datdo-is-coding/Home-Assistant-IoT-/Hardware/PCB/IoT_Board/erc_report.txt

ERC report (2026-08-20T07:09:29, Encoding UTF8)
Report includes: Errors, Warnings, Exclusions

***** Sheet /
[power_pin_not_driven]: Input Power pin not driven by any Output Power pins
    ; error
    @(25.40 mm, 194.31 mm): Symbol #PWR084 Pin 1 [Power input, Line]
[power_pin_not_driven]: Input Power pin not driven by any Output Power pins
    ; error
    @(80.01 mm, 100.33 mm): Symbol #PWR02 Pin 1 [Power input, Line]
[power_pin_not_driven]: Input Power pin not driven by any Output Power pins
    ; error
    @(309.88 mm, 248.92 mm): Symbol #PWR050 Pin 1 [Power input, Line]
[power_pin_not_driven]: Input Power pin not driven by any Output Power pins
    ; error
    @(377.19 mm, 243.84 mm): Symbol U4 Pin 1 [AC/L, Power input, Line]
[power_pin_not_driven]: Input Power pin not driven by any Output Power pins
    ; error
    @(377.19 mm, 248.92 mm): Symbol U4 Pin 2 [AC/N, Power input, Line]
[power_pin_not_driven]: Input Power pin not driven by any Output Power pins
    ; error
    @(401.32 mm, 191.77 mm): Symbol #PWR020 Pin 1 [Power input, Line]
[same_local_global_label]: Local and global labels have same name
    ; warning
    @(38.10 mm, 171.45 mm): Global Label 'RS'
    @(55.88 mm, 77.47 mm): Label 'RS'
[same_local_global_label]: Local and global labels have same name
    ; warning
    @(40.64 mm, 166.37 mm): Global Label 'CS'
    @(55.88 mm, 80.01 mm): Label 'CS'
[same_local_global_label]: Local and global labels have same name
    ; warning
    @(40.64 mm, 196.85 mm): Global Label 'DIN'
    @(55.88 mm, 82.55 mm): Label 'DIN'
[same_local_global_label]: Local and global labels have same name
    ; warning
    @(40.64 mm, 199.39 mm): Global Label 'SCLK'
    @(55.88 mm, 85.09 mm): Label 'SCLK'
[footprint_link_issues]: The current configuration does not include the footprint library 'ADS'
    ; warning
    @(69.85 mm, 194.31 mm): Symbol U14 [ADS1256IDBR]
[same_local_global_label]: Local and global labels have same name
    ; warning
    @(96.52 mm, 166.37 mm): Global Label 'DRDY'
    @(55.88 mm, 90.17 mm): Label 'DRDY'
[same_local_global_label]: Local and global labels have same name
    ; warning
    @(96.52 mm, 168.91 mm): Global Label 'DO'
    @(55.88 mm, 87.63 mm): Label 'DO'
[multiple_net_names]: Both VREFP and V_Bias are attached to the same items; VREFP will be used in the netlist
    ; warning
    @(36.83 mm, 204.47 mm): Label 'VREFP'
    @(127.00 mm, 148.59 mm): Label 'V_Bias'
[lib_symbol_mismatch]: Symbol 'Conn_01x07_Pin' doesn't match copy in library 'Connector'
    ; warning
    @(182.88 mm, 67.31 mm): Symbol J14 [Conn_01x07_Pin]
[lib_symbol_mismatch]: Symbol 'Conn_02x03_Counter_Clockwise' doesn't match copy in library 'Connector_Generic'
    ; warning
    @(191.77 mm, 91.44 mm): Symbol J15 [Conn_02x03_Counter_Clockwise]
[footprint_link_issues]: The current configuration does not include the footprint library ''
    ; warning
    @(232.41 mm, 29.21 mm): Symbol IC1 [VS1838B]
[footprint_link_issues]: The current configuration does not include the footprint library 'B050S'
    ; warning
    @(309.88 mm, 241.30 mm): Symbol PS1 [B0505S-2W]
[footprint_link_issues]: The current configuration does not include the footprint library 'PC817_SMD'
    ; warning
    @(316.23 mm, 38.10 mm): Symbol U7 [PC817]
[footprint_link_issues]: The current configuration does not include the footprint library 'PC817_SMD'
    ; warning
    @(317.50 mm, 74.93 mm): Symbol U6 [PC817]
[footprint_link_issues]: The current configuration does not include the footprint library 'PC817_SMD'
    ; warning
    @(317.50 mm, 114.30 mm): Symbol U5 [PC817]
[footprint_link_issues]: The current configuration does not include the footprint library 'RL10SRD'
    ; warning
    @(369.57 mm, 29.21 mm): Symbol K3 [SRD-12VDC-SL-C]
[lib_symbol_issues]: The current configuration does not include the symbol library 'RL10ASRD'
    ; warning
    @(369.57 mm, 29.21 mm): Symbol K3 [SRD-12VDC-SL-C]
[footprint_link_issues]: The current configuration does not include the footprint library 'RL10SRD'
    ; warning
    @(370.84 mm, 66.04 mm): Symbol K2 [SRD-12VDC-SL-C]
[lib_symbol_issues]: The current configuration does not include the symbol library 'RL10ASRD'
    ; warning
    @(370.84 mm, 66.04 mm): Symbol K2 [SRD-12VDC-SL-C]
[footprint_link_issues]: The current configuration does not include the footprint library 'RL10SRD'
    ; warning
    @(370.84 mm, 105.41 mm): Symbol K1 [SRD-12VDC-SL-C]
[lib_symbol_issues]: The current configuration does not include the symbol library 'RL10ASRD'
    ; warning
    @(370.84 mm, 105.41 mm): Symbol K1 [SRD-12VDC-SL-C]
[multiple_net_names]: Both +5VD and USB_V are attached to the same items; +5VD will be used in the netlist
    ; warning
    @(248.92 mm, 57.15 mm): Symbol #PWR0116 Pin 1 [Power input, Line]
    @(375.92 mm, 167.64 mm): Label 'USB_V'
[footprint_link_issues]: The current configuration does not include the footprint library 'KH-TYPE-C-16P'
    ; warning
    @(383.54 mm, 191.77 mm): Symbol J3 [KH-TYPE-C-16P]
[lib_symbol_issues]: The current configuration does not include the symbol library 'KH-TYPE-C-16P'
    ; warning
    @(383.54 mm, 191.77 mm): Symbol J3 [KH-TYPE-C-16P]

 ** ERC messages: 30  Errors 6  Warnings 24

 ** Ignored checks:
    - Global label only appears once in the schematic
    - Four connection points are joined together
    - SPICE model issue
    - Assigned footprint doesn't match footprint filters
