datdo-is-coding/Home-Assistant-IoT-/App/dtv_energy_flutter/test/goldens/home.png

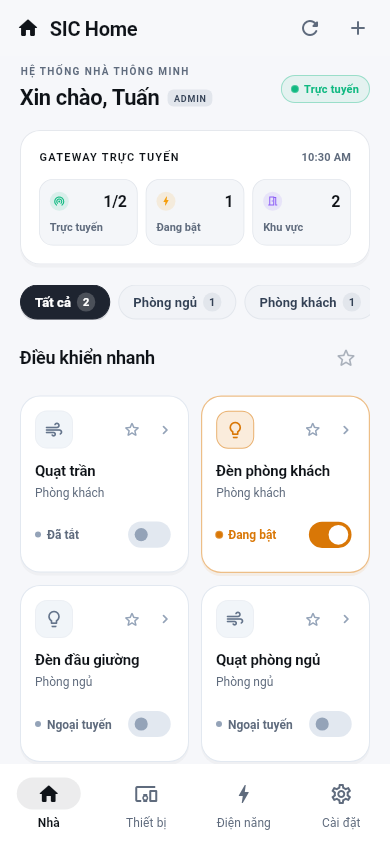
App/dtv_energy_flutter/test/goldens/home.png
