datdo-is-coding/Home-Assistant-IoT-/App/dtv_energy_flutter/test/goldens/settings.png

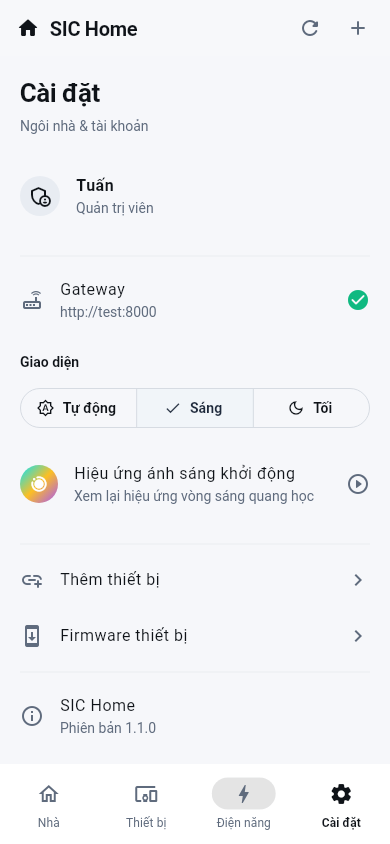
App/dtv_energy_flutter/test/goldens/settings.png
