datdo-is-coding/Home-Assistant-IoT-/Gateway/gateway/intent_engine.py

"""
Intent Engine v3 — Hệ thống phân tích ý định khẩu lệnh tiếng Việt (Production-Ready for Raspberry Pi 4)
===================================================================================================

Triết lý kiến trúc chuẩn:
    ASR ≠ Intent ≠ Device ≠ Node ≠ Execution ≠ Response

Pipeline:
    ASR text
       ↓
    ASR Normalizer (âm vị, độ tin cậy, không phá vỡ ngữ cảnh)
       ↓
    Negation Detector (chặn câu phủ định, không biến thành turn_on)
       ↓
    Fast Path / Rule Engine (phân cấp HIGH / MEDIUM / AMBIGUOUS)
       ↓ (nếu HIGH ≥ 0.95 → bypass LLM)
    Context Resolver (Multi-turn Context với TTL, kế thừa an toàn)
       ↓ (nếu cần LLM / phức tạp)
    LLM NLU Engine (Gemini Flash Cloud / Local Qwen 2.5 với prompt siêu gọn & GBNF)
       ↓
    Intent Normalization
       ↓
    Strict Validator (đối chiếu Registry: Exact → Alias → Unique Fuzzy → Reject)
       ↓
    IntentResult (Dữ liệu cấu trúc + tương thích ngược dictionary)

Nguyên tắc bất biến:
- Intent Engine KHÔNG điều khiển GPIO, KHÔNG quyết định node_id/channel
- Intent Engine KHÔNG hallucinate thiết bị/phòng ngoài Registry
- Intent Engine KHÔNG tự nhận định command thành công trước khi Verifier/MQTT trả kết quả
- Response hoàn tất ("Dạ em đã bật...") chỉ do Verifier/Response Generator sinh sau khi ESP32 thực thi
"""

import json
import logging
import re
import time
from dataclasses import dataclass, field
from typing import Optional, Dict, Any, List, Tuple

try:
    import httpx
except ImportError:
    httpx = None

import config
from display_names import get_room_name, get_device_name, clean_voice_text

logger = logging.getLogger("intent")


# ── BẢNG TỪ ĐIỂN VÀ ALIASES CHUẨN HOÁ ────────────────────────────────────────

def slug(s: Optional[str]) -> str:
    """Chuyển đổi chuỗi tiếng Việt có dấu thành slug không dấu dạng snake_case."""
    if s is None:
        return ""
    s = str(s).lower().strip()
    tbl = str.maketrans(
        "áàảãạăắằẳẵặâấầẩẫậéèẻẽẹêếềểễệíìỉĩịóòỏõọôốồổỗộơớờởỡợúùủũụưứừửữựýỳỷỹỵđ",
        "aaaaaaaaaaaaaaaaaeeeeeeeeeeeiiiiiooooooooooooooooouuuuuuuuuuuyyyyyd"
    )
    s = s.translate(tbl)
    s = re.sub(r"[^a-z0-9]+", "_", s).strip("_")
    return s


# Danh mục thiết bị chuẩn (Canonical Device Mapping)
DEVICE_ALIASES: Dict[str, List[str]] = {
    "light": [
        "đèn", "bóng đèn", "đèn điện", "ánh sáng", "light", "den", "bong_den",
        "đèn trần", "den_tran", "đèn chùm", "đèn tuýp", "đèn led", "đèn bàn", "đèn học"
    ],
    "den_ngu": [
        "đèn ngủ", "den_ngu", "đèn đầu giường", "den ngu"
    ],
    "fan": [
        "quạt", "quạt điện", "quạt máy", "quat", "fan",
        "quạt trần", "quạt cây", "quạt đứng", "quạt bàn", "quạt treo", "quạt thông gió"
    ],
    "air_conditioner": [
        "điều hòa", "máy lạnh", "máy điều hòa", "dieu_hoa", "may_lanh", "ac",
        "air conditioner", "air_conditioner", "máy lạng", "máy lặng"
    ],
    "pump": [
        "máy bơm", "bơm", "máy tưới", "tưới cây", "tưới", "pump", "may_bom"
    ],
    "curtain": [
        "rèm", "rèm cửa", "màn", "màn cửa", "curtain", "rem"
    ],
    "tivi": [
        "tivi", "ti vi", "tv", "television"
    ],
    "binh_nong_lanh": [
        "bình nóng lạnh", "bình nước nóng", "nước nóng", "binh_nong_lanh"
    ],
    "may_hut_mui": [
        "hút mùi", "máy hút mùi", "may_hut_mui", "quạt hút mùi"
    ],
    "socket": [
        "ổ cắm", "o_cam", "ổ điện", "phích cắm", "socket", "ổ", "o cam", "o dien",
        "ổ cắm điện", "phích cắm điện"
    ],
    "ch1": [
        "relay 1", "relay một", "công tắc 1", "công tắc một", "kênh 1", "kênh một", "nút 1"
    ],
    "ch2": [
        "relay 2", "relay hai", "công tắc 2", "công tắc hai", "kênh 2", "kênh hai", "nút 2"
    ],
    "all": [
        "tất cả", "toàn bộ", "hết", "toàn bộ thiết bị", "tất cả thiết bị"
    ]
}

# Danh mục phòng chuẩn (Canonical Room Mapping)
ROOM_ALIASES: Dict[str, List[str]] = {
    "phong_ngu": [
        "phòng ngủ", "phong ngu", "ngủ", "bedroom", "p_ngu"
    ],
    "phong_ngu_master": [
        "phòng ngủ master", "phòng master", "ngủ master", "master bedroom"
    ],
    "phong_ngu_con": [
        "phòng ngủ con", "ngủ con", "phòng con"
    ],
    "phong_khach": [
        "phòng khách", "phong khach", "khách", "living room", "livingroom", "p_khach"
    ],
    "phong_bep": [
        "phòng bếp", "phong bep", "bếp", "nhà bếp", "kitchen", "p_bep"
    ],
    "phong_tam": [
        "nhà vệ sinh", "vệ sinh", "toilet", "wc", "phòng tắm", "bathroom", "tắm", "phong_ve_sinh"
    ],
    "ban_cong": [
        "ban công", "balcony"
    ],
    "san_thuong": [
        "sân thượng", "rooftop"
    ],
    "san_vuon": [
        "sân vườn", "ngoài sân", "vườn", "garden", "san vuon"
    ],
    "gara": [
        "gara", "nhà xe", "ga ra", "garage"
    ],
    "phong_tho": [
        "phòng thờ"
    ],
    "phong_lam_viec": [
        "phòng làm việc", "làm việc", "phòng học"
    ],
    "hanh_lang": [
        "hành lang", "cầu thang"
    ]
}

# Bảng số từ tiếng Việt biểu diễn nhiệt độ điều hòa (16 - 32 độ C)
VIETNAMESE_NUMBERS: Dict[str, int] = {
    "mười sáu": 16, "mười bảy": 17, "mười tám": 18, "mười chín": 19,
    "hai mươi": 20, "hai mốt": 21, "hai mươi mốt": 21,
    "hai hai": 22, "hai mươi hai": 22,
    "hai ba": 23, "hai mươi ba": 23,
    "hai tư": 24, "hai bốn": 24, "hai mươi tư": 24, "hai mươi bốn": 24,
    "hai lăm": 25, "hai năm": 25, "hai mươi lăm": 25, "hai mươi năm": 25,
    "hai sáu": 26, "hai mươi sáu": 26,
    "hai bảy": 27, "hai mươi bảy": 27,
    "hai tám": 28, "hai mươi tám": 28,
    "hai chín": 29, "hai mươi chín": 29,
    "ba mươi": 30, "ba chục": 30,
    "ba mốt": 31, "ba mươi mốt": 31,
    "ba hai": 32, "ba mươi hai": 32
}


# ── DATA STRUCTURES & INTENT RESULT ──────────────────────────────────────────

@dataclass
class Target:
    """Mục tiêu điều khiển của Intent (Device Type, Specific Name, Room)."""
    device_type: Optional[str] = None
    device_name: Optional[str] = None
    room: Optional[str] = None

    def to_dict(self) -> Dict[str, Optional[str]]:
        return {
            "device_type": self.device_type,
            "device_name": self.device_name,
            "room": self.room,
        }


@dataclass
class NormalizedText:
    """Kết quả sau khi chuẩn hóa âm vị và phát hiện lỗi ASR."""
    text: str
    original_text: str
    corrections: List[Dict[str, str]] = field(default_factory=list)
    confidence: float = 1.0


class IntentResult(dict):
    """
    Kết quả ý định trích xuất chuẩn hoá v3.
    Đồng thời kế thừa dict để tương thích ngược hoàn toàn 100% với:
    - main.py: intent["command"]["action"], intent["command"]["device"], intent["voice_reply"]
    - evaluator.py: raw_intent["command"]
    """
    def __init__(
        self,
        intent: str,
        target: Optional[Target] = None,
        value: Optional[Any] = None,
        unit: Optional[str] = None,
        confidence: float = 1.0,
        source: str = "fast_path",
        needs_clarification: bool = False,
        clarification_reason: Optional[str] = None,
        negated: bool = False,
        raw_text: str = "",
        normalized_text: str = "",
        voice_reply: Optional[str] = None,
        commands: Optional[List["IntentResult"]] = None,
        scene: Optional[str] = None,
        **extra
    ):
        super().__init__()
        self.intent = intent
        self.target = target or Target()
        self.value = value
        self.unit = unit
        self.confidence = float(confidence)
        self.source = source
        self.needs_clarification = needs_clarification
        self.clarification_reason = clarification_reason
        self.negated = negated
        self.raw_text = raw_text
        self.normalized_text = normalized_text
        self.voice_reply = voice_reply
        self.commands = commands or []
        self.scene = scene

        self._sync_dict()

    def _sync_dict(self):
        """Cập nhật các key từ điển để bảo đảm tương thích ngược với main.py."""
        action = self.intent
        if self.intent in ("set_temperature", "set_value"):
            action = "set_value"
        elif self.intent in ("query_state", "query_sensor", "scene"):
            action = self.intent
        elif self.intent not in ("turn_on", "turn_off", "unknown"):
            action = "unknown"

        self["intent"] = self.intent
        self["target"] = self.target.to_dict()
        self["value"] = self.value
        self["unit"] = self.unit
        self["confidence"] = self.confidence
        self["source"] = self.source
        self["needs_clarification"] = self.needs_clarification
        self["clarification_reason"] = self.clarification_reason
        self["negated"] = self.negated
        self["raw_text"] = self.raw_text
        self["normalized_text"] = self.normalized_text
        self["scene"] = self.scene
        self["commands"] = [
            cmd.to_dict() if isinstance(cmd, IntentResult) else cmd for cmd in self.commands
        ]
        self["voice_reply"] = self.voice_reply

        # Legacy command object format mong đợi bởi main.py
        self["command"] = {
            "action": action,
            "device": self.target.device_type,
            "location": self.target.room,
            "value": self.value
        }

    def to_dict(self) -> Dict[str, Any]:
        self._sync_dict()
        return dict(self)

    def __repr__(self) -> str:
        return (
            f"IntentResult(intent='{self.intent}', target={self.target.to_dict()}, "
            f"val={self.value}, conf={self.confidence:.2f}, src='{self.source}', "
            f"clarify={self.needs_clarification}, negated={self.negated})"
        )


# ── MODULE 1: ASR NORMALIZER ─────────────────────────────────────────────────

class ASRNormalizer:
    """
    Module chuẩn hóa âm vị và khắc phục lỗi ASR tiếng Việt chuyên sâu.
    Tách biệt hoàn toàn khỏi logic trích xuất ý định.
    Ghi nhận confidence và danh sách corrections.
    """
    def __init__(self):
        self.phonetic_rules: List[Tuple[str, str, float, str]] = [
            # Lỗi đặc thù nghiêm trọng của ASR: "bạn bè" -> "bật đèn"
            (r"\bbạn bè phòng\b", "bật đèn phòng", 0.96, "bạn bè phòng → bật đèn phòng"),
            (r"\bbạn bè\b", "bật đèn", 0.95, "bạn bè → bật đèn"),
            (r"\bbạn về\b", "bật đèn", 0.94, "bạn về → bật đèn"),
            (r"\bbạn đề\b", "bật đèn", 0.94, "bạn đề → bật đèn"),

            # Họ âm vị quạt: "bất quá / bật quà / bật quát" -> "bật quạt"
            (r"\bbất quá\b", "bật quạt", 0.95, "bất quá → bật quạt"),
            (r"\bbật quà\b", "bật quạt", 0.95, "bật quà → bật quạt"),
            (r"\bbật quát\b", "bật quạt", 0.95, "bật quát → bật quạt"),
            (r"\bbắt quạt\b", "bật quạt", 0.95, "bắt quạt → bật quạt"),
            (r"\bbật quét\b", "bật quạt", 0.94, "bật quét → bật quạt"),
            (r"\bbất quạt\b", "bật quạt", 0.95, "bất quạt → bật quạt"),
            (r"\bmở quá\b", "mở quạt", 0.95, "mở quá → mở quạt"),
            (r"\bmở quà\b", "mở quạt", 0.95, "mở quà → mở quạt"),
            (r"\btắt quá\b", "tắt quạt", 0.95, "tắt quá → tắt quạt"),
            (r"\btắt quà\b", "tắt quạt", 0.95, "tắt quà → tắt quạt"),

            # Họ âm vị đèn
            (r"\bbật điên\b", "bật đèn", 0.95, "bật điên → bật đèn"),
            (r"\btắt điên\b", "tắt đèn", 0.95, "tắt điên → tắt đèn"),
            (r"\bbật đền\b", "bật đèn", 0.95, "bật đền → bật đèn"),
            (r"\btắt đền\b", "tắt đèn", 0.95, "tắt đền → tắt đèn"),
            (r"\bbật đêm\b", "bật đèn", 0.95, "bật đêm → bật đèn"),
            (r"\btắt đêm\b", "tắt đèn", 0.95, "tắt đêm → tắt đèn"),
            (r"\bbạt đèn\b", "bật đèn", 0.96, "bạt đèn → bật đèn"),
            (r"\bbạt đền\b", "bật đèn", 0.95, "bạt đền → bật đèn"),
            (r"\btác đèn\b", "tắt đèn", 0.95, "tác đèn → tắt đèn"),

            # Họ điều hòa / máy lạnh
            (r"\bmáy lặng\b", "máy lạnh", 0.97, "máy lặng → máy lạnh"),
            (r"\bmáy lạng\b", "máy lạnh", 0.97, "máy lạng → máy lạnh"),
            (r"\bđiều hoà\b", "điều hòa", 0.99, "điều hoà → điều hòa"),
            (r"\bmáy điều hòa\b", "điều hòa", 0.99, "máy điều hòa → điều hòa"),

            # Phòng
            (r"\bphòng ngue\b", "phòng ngủ", 0.96, "phòng ngue → phòng ngủ"),
            (r"\bphòng nghủ\b", "phòng ngủ", 0.96, "phòng nghủ → phòng ngủ"),
            (r"\bphòng khash\b", "phòng khách", 0.96, "phòng khash → phòng khách"),
            (r"\bphòng khác\b", "phòng khách", 0.92, "phòng khác → phòng khách"),
            (r"\bphòng bép\b", "phòng bếp", 0.96, "phòng bép → phòng bếp"),
            (r"\bnhà bép\b", "nhà bếp", 0.96, "nhà bép → nhà bếp"),

            # Đồng nghĩa thiết bị
            (r"\bquạt điện\b", "quạt", 0.98, "quạt điện → quạt"),
            (r"\bquạt máy\b", "quạt", 0.98, "quạt máy → quạt"),
            (r"\bbóng đèn\b", "đèn", 0.98, "bóng đèn → đèn"),

            # Lỗi nhầm lẫn âm học đặc thù từ Zipformer ASR
            (r"\bban đêm không ngủ\b", "bật quạt phòng ngủ", 0.98, "ban đêm không ngủ → bật quạt phòng ngủ"),
            (r"\bđêm qua không ngủ\b", "bật quạt phòng ngủ", 0.98, "đêm qua không ngủ → bật quạt phòng ngủ"),
            (r"\bkhông ngủ\b", "phòng ngủ", 0.96, "không ngủ → phòng ngủ"),
            (r"\bkhong ngu\b", "phòng ngủ", 0.96, "khong ngu → phòng ngủ"),
            (r"\bhòng ngủ\b", "phòng ngủ", 0.96, "hòng ngủ → phòng ngủ"),
            (r"\bphòng ngũ\b", "phòng ngủ", 0.96, "phòng ngũ → phòng ngủ"),
            (r"\bđêm qua\b", "bật quạt", 0.95, "đêm qua → bật quạt"),
            (r"\bban đêm\b", "bật đèn", 0.95, "ban đêm → bật đèn"),
            (r"\bbật qua\b", "bật quạt", 0.95, "bật qua → bật quạt"),
            (r"\bbắt quạt\b", "bật quạt", 0.95, "bắt quạt → bật quạt"),
            (r"\btắt qua\b", "tắt quạt", 0.95, "tắt qua → tắt quạt"),
            (r"\btác quạt\b", "tắt quạt", 0.95, "tác quạt → tắt quạt"),
        ]

        self.noise_fillers = [
            r"\b(ừm|ơ|à|ờ|hmm|uh|ơi|nhé|nha|giúp|hộ|cho tui|cho mình|cho tôi|làm ơn)\b"
        ]

    def normalize(self, raw_text: str) -> NormalizedText:
        if not raw_text or not raw_text.strip():
            return NormalizedText(text="", original_text="", confidence=1.0)

        cleaned = raw_text.lower().strip()
        corrections: List[Dict[str, str]] = []
        accumulated_confidence = 1.0

        for pattern, replacement, conf, desc in self.phonetic_rules:
            if re.search(pattern, cleaned):
                cleaned = re.sub(pattern, replacement, cleaned)
                corrections.append({"rule": desc, "confidence": conf})
                accumulated_confidence = min(accumulated_confidence, conf)

        for filler in self.noise_fillers:
            cleaned = re.sub(filler, " ", cleaned)

        cleaned = re.sub(r"\s+", " ", cleaned).strip()

        return NormalizedText(
            text=cleaned,
            original_text=raw_text,
            corrections=corrections,
            confidence=accumulated_confidence
        )


# ── MODULE 2: NEGATION DETECTOR ──────────────────────────────────────────────

class NegationDetector:
    """
    Nhận diện câu phủ định để TUYỆT ĐỐI KHÔNG chuyển thành hành động kích hoạt.
    Ví dụ: 'đừng bật đèn', 'không bật quạt', 'tôi không muốn bật điều hòa'.
    """
    NEGATION_TRIGGERS = [
        r"\bđừng\b",
        r"\bkhông\b",
        r"\bchớ\b",
        r"\bkhông được\b",
        r"\bkhông cần\b",
        r"\bchẳng cần\b",
        r"\btôi không muốn\b",
        r"\bchưa muốn\b",
        r"\bđừng có\b",
    ]

    @classmethod
    def is_negated(cls, text: str) -> bool:
        t = text.lower()
        for pattern in cls.NEGATION_TRIGGERS:
            if re.search(pattern + r"\s+(?:bật|mở|khởi động|kích hoạt|cài|đặt|chỉnh|tăng|hạ|cho|làm)", t):
                return True
            if re.search(r"nhưng\s+" + pattern, t):
                return True
            if re.search(r"mà\s+" + pattern, t):
                return True
        return False


# ── MODULE 3: MULTI-TURN CONTEXT MANAGER ─────────────────────────────────────

class IntentContextManager:
    """
    Quản lý ngữ cảnh đối thoại đa lượt (Multi-Turn Context) với TTL.
    Kế thừa thông tin một cách an toàn và ngăn chặn suy diễn vô hạn.
    """
    def __init__(self, ttl_seconds: float = 60.0):
        self.ttl_seconds = ttl_seconds
        self.last_device_type: Optional[str] = None
        self.last_room: Optional[str] = None
        self.last_intent: Optional[str] = None
        self.last_value: Optional[Any] = None
        self.updated_at: float = 0.0

    @property
    def is_valid(self) -> bool:
        return (time.time() - self.updated_at) <= self.ttl_seconds and self.updated_at > 0

    def update(self, result: IntentResult):
        """Cập nhật ngữ cảnh khi có một lệnh rõ ràng."""
        if result.intent in ("turn_on", "turn_off", "set_temperature", "set_value"):
            if result.target.device_type:
                self.last_device_type = result.target.device_type
            if result.target.room:
                self.last_room = result.target.room
            self.last_intent = result.intent
            if result.value is not None:
                self.last_value = result.value
            self.updated_at = time.time()
            logger.debug(
                f"🧠 [Context Updated] device={self.last_device_type}, "
                f"room={self.last_room}, intent={self.last_intent}, val={self.last_value}"
            )

    def resolve(self, raw_intent: IntentResult, raw_user_text: str) -> IntentResult:
        """
        Bổ sung các slot thiếu thông qua ngữ cảnh hợp lệ gần nhất.
        """
        if not self.is_valid:
            return raw_intent

        text = raw_user_text.lower()
        has_pronoun = bool(re.search(r"\b(nó|cái này|cái kia|cái đó|thiết bị đó|ở đó)\b", text))
        is_bare_action = not raw_intent.target.device_type and raw_intent.intent in ("turn_on", "turn_off", "toggle") and len(text.strip().split()) <= 3

        # Trường hợp 1: Đại từ thay thế hoặc lệnh ngắn ("bật nó lên", "tắt nó đi", "tắt", "bật")
        if (has_pronoun or is_bare_action) and self.last_device_type:
            if not raw_intent.target.device_type:
                raw_intent.target.device_type = self.last_device_type
            if not raw_intent.target.room and self.last_room:
                raw_intent.target.room = self.last_room
            raw_intent.source = "context"
            raw_intent.confidence = 0.92
            raw_intent.needs_clarification = False
            raw_intent.clarification_reason = None
            raw_intent._sync_dict()
            return raw_intent

        # Trường hợp 2: Lệnh cài đặt nhiệt độ thiếu thiết bị/phòng ("Cài 25 độ", "Tăng lên 26 độ")
        if raw_intent.intent in ("set_temperature", "set_value"):
            if self.last_device_type in ("air_conditioner", "dieu_hoa", "may_lanh"):
                if not raw_intent.target.device_type:
                    raw_intent.target.device_type = "air_conditioner"
                if not raw_intent.target.room and self.last_room:
                    raw_intent.target.room = self.last_room
                raw_intent.source = "context"
                raw_intent.confidence = 0.95
                raw_intent.needs_clarification = False
                raw_intent.clarification_reason = None
                raw_intent._sync_dict()
                return raw_intent

        # Trường hợp 3: Nguyên tắc an toàn CHỐNG suy diễn vô hạn:
        # Nếu người dùng đổi sang thiết bị khác (ví dụ trước đó 'Bật đèn phòng ngủ', giờ 'Bật quạt')
        # Tuyệt đối KHÔNG tự ý gán quạt vào phòng ngủ nếu người dùng không nói rõ!
        if raw_intent.target.device_type and raw_intent.target.device_type != self.last_device_type:
            pass

        return raw_intent

    def clear(self):
        self.last_device_type = None
        self.last_room = None
        self.last_intent = None
        self.last_value = None
        self.updated_at = 0.0


# ── MODULE 4: STRICT VALIDATOR ───────────────────────────────────────────────

class StrictValidator:
    """
    Xác thực nghiêm ngặt đối chiếu với Registry thực tế.
    Loại bỏ hoàn toàn các heuristic kiểm tra độ dài len(s) > 20.
    Thứ tự: Exact Match -> Alias Match -> Unique Fuzzy Match -> Reject.
    """
    def __init__(self, registry=None):
        self.registry = registry

    def set_registry(self, registry):
        self.registry = registry

    def resolve_room(self, room_input: Optional[str]) -> Tuple[Optional[str], bool]:
        """
        Trả về (canonical_room, is_ambiguous).
        Nếu không tìm thấy hoặc hallucinated -> (None, False).
        """
        if not room_input:
            return None, False

        r_slug = slug(room_input)
        allowed_rooms = set(self.registry.allowed_rooms()) if self.registry else set(ROOM_ALIASES.keys())

        # 1. Exact match
        if r_slug in allowed_rooms:
            return r_slug, False

        # 2. Alias match
        for canon, aliases in ROOM_ALIASES.items():
            if canon in allowed_rooms or not self.registry:
                for a in aliases:
                    if r_slug == slug(a) or slug(a) == r_slug:
                        return canon, False

        # 3. Unique Fuzzy match (khoảng cách sai biệt 1 ký tự hoặc tiền tố duy nhất)
        candidates = []
        for ar in allowed_rooms:
            if ar.startswith(r_slug) or r_slug.startswith(ar):
                candidates.append(ar)
        if len(candidates) == 1:
            return candidates[0], False
        elif len(candidates) > 1:
            return None, True

        # 4. Hallucination / Không tồn tại
        return None, False

    def resolve_device(self, device_input: Optional[str]) -> Tuple[Optional[str], bool]:
        """
        Trả về (canonical_device, is_ambiguous).
        Nếu không tìm thấy hoặc hallucinated -> (None, False).
        """
        if not device_input:
            return None, False

        d_slug = slug(device_input)
        allowed_devs = set(self.registry.allowed_devices()) if self.registry else set(DEVICE_ALIASES.keys())

        # 1. Exact match
        if d_slug in allowed_devs:
            return d_slug, False

        # 2. Alias match
        for canon, aliases in DEVICE_ALIASES.items():
            for a in aliases:
                if d_slug == slug(a):
                    target_dev = "light" if canon in ("den", "bong_den") else canon
                    return target_dev, False

        # 3. Unique Fuzzy match
        candidates = []
        for ad in allowed_devs:
            if ad.startswith(d_slug) or d_slug.startswith(ad):
                candidates.append(ad)
        if len(candidates) == 1:
            return candidates[0], False
        elif len(candidates) > 1:
            return None, True

        # 4. Hallucination
        return None, False

    def validate(self, result: IntentResult) -> IntentResult:
        """Thực thi kiểm định nghiêm ngặt trên IntentResult."""
        if not self.registry:
            return result

        # Validate Room
        if result.target.room:
            clean_r, is_ambig = self.resolve_room(result.target.room)
            if clean_r:
                result.target.room = clean_r
            elif is_ambig:
                result.target.room = None
                result.needs_clarification = True
                result.clarification_reason = "ambiguous_room"
            else:
                logger.warning(f"🚫 [StrictValidator] Rejected hallucinated room '{result.target.room}'")
                result.target.room = None
                result.needs_clarification = True
                result.clarification_reason = "unregistered_room"

        # Validate Device
        if result.target.device_type and result.target.device_type != "all":
            clean_d, is_ambig = self.resolve_device(result.target.device_type)
            if clean_d:
                result.target.device_type = clean_d
            elif is_ambig:
                result.target.device_type = None
                result.needs_clarification = True
                result.clarification_reason = "ambiguous_device"
            else:
                logger.warning(f"🚫 [StrictValidator] Rejected hallucinated device '{result.target.device_type}'")
                result.target.device_type = None
                result.needs_clarification = True
                result.clarification_reason = "unregistered_device"

        result._sync_dict()
        return result


# ── MODULE 5: FAST PATH ENGINE ───────────────────────────────────────────────
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
