datdo-is-coding/Home-Assistant-IoT-/Gateway/gateway/registry_manager.py

"""
Device Registry Manager v2 — quản lý theo phòng + fullname + provision flow.

- Mỗi node: id = {room}-{short}  e.g. livingroom-node01, bedroom-node02
- Mỗi relay: fullname = {node_id}-{dev} e.g. livingroom-node01-light
- ESP32 lưu {node_id, room, rl1, rl2, cfg_version} vào NVS và echo lại mỗi hello.
- Node mới (cfg==null) vào hàng chờ pending → WebUI đăng ký → Gateway gửi cfg.

Tương thích ngược: tự migrate file cũ (area/channels) sang schema mới khi load.
"""
import json
import os
import re
import sqlite3
import logging
from contextlib import contextmanager, nullcontext
from datetime import datetime, timezone, timedelta
from typing import Optional, Dict, Any, List, Tuple

import config

logger = logging.getLogger("registry")
TZ_VN = timezone(timedelta(hours=7))

# ── Chuẩn hoá ────────────────────────────────────────────────────────────────
_slug_re = re.compile(r"[^a-z0-9]+")
_slug_translation = str.maketrans(
    "áàảãạăắằẳẵặâấầẩẫậéèẻẽẹêếềểễệíìỉĩịóòỏõọôốồổỗộơớờởỡợúùủũụưứừửữựýỳỷỹỵđ",
    "aaaaaaaaaaaaaaaaaeeeeeeeeeeeiiiiiooooooooooooooooouuuuuuuuuuuyyyyyd",
)
def slug(s: str) -> str:
    s = (s or "").lower().strip()
    # bỏ dấu tiếng Việt cơ bản
    s = s.translate(_slug_translation)
    s = _slug_re.sub("_", s).strip("_")
    return s or "unknown"

DEVICE_CANON = {
    "den": "light", "light": "light", "bong_den": "light",
    "quat": "fan", "fan": "fan",
    "bom": "pump", "may_bom": "pump", "pump": "pump",
    "rem": "curtain", "man": "curtain",
}
def canon_device(s: str) -> str:
    s = slug(s)
    return DEVICE_CANON.get(s, s)

ROOM_ALIASES = {
    "phong_khach": ["phong_khach", "livingroom", "living_room", "khach", "p_khach"],
    "phong_ngu":   ["phong_ngu", "bedroom", "ngu", "p_ngu"],
    "phong_bep":   ["phong_bep", "kitchen", "bep"],
    "phong_tam":   ["phong_tam", "bathroom", "tam", "wc"],
    "ban_cong":    ["ban_cong", "balcony"],
    "san_vuon":    ["san_vuon", "garden", "vuon"],
}

class RegistryManager:
    def __init__(self, registry_path: str = None, db_path: str = None):
        self.path = registry_path or config.REGISTRY_FILE
        self.db_path = db_path or getattr(config, "GATEWAY_DB", "/var/lib/smarthome/gateway.db")
        try:
            os.makedirs(os.path.dirname(os.path.abspath(self.db_path)), exist_ok=True)
        except Exception:
            pass
        self.data: Dict[str, Any] = {"nodes": {}, "pending": {}, "rooms": {}}
        self._seq: Dict[str, int] = {}  # node_id -> last seq
        self._persisted = {}
        self._init_sqlite()
        self.load()

    # ── SQLite Database Storage Engine (Spec Section 8) ──────────────────
    @contextmanager
    def _get_db(self):
        conn = sqlite3.connect(self.db_path, timeout=10.0)
        conn.row_factory = sqlite3.Row
        conn.execute("PRAGMA journal_mode = WAL;")
        conn.execute("PRAGMA foreign_keys = ON;")
        try:
            with conn:
                yield conn
        finally:
            conn.close()

    def _init_sqlite(self):
        try:
            with self._get_db() as conn:
                conn.executescript("""
                CREATE TABLE IF NOT EXISTS registry_entries (
                    kind TEXT NOT NULL, entry_id TEXT NOT NULL, payload TEXT NOT NULL,
                    PRIMARY KEY(kind, entry_id)
                );
                CREATE TABLE IF NOT EXISTS registry_meta (key TEXT PRIMARY KEY, value TEXT NOT NULL);
                CREATE TABLE IF NOT EXISTS rooms (
                    room_id VARCHAR(32) PRIMARY KEY,
                    display_name VARCHAR(64) NOT NULL,
                    floor_level INTEGER DEFAULT 1,
                    created_at DATETIME DEFAULT CURRENT_TIMESTAMP
                );

                CREATE TABLE IF NOT EXISTS devices (
                    device_id VARCHAR(32) PRIMARY KEY,
                    hardware_id VARCHAR(32) NOT NULL,
                    serial_number VARCHAR(32) UNIQUE NOT NULL,
                    device_type VARCHAR(24) NOT NULL,
                    name VARCHAR(64) NOT NULL,
                    room_id VARCHAR(32),
                    location VARCHAR(128),
                    description TEXT,
                    mac_address VARCHAR(18) NOT NULL,
                    ip_address VARCHAR(15),
                    rssi INTEGER,
                    status VARCHAR(16) DEFAULT 'UNPROVISIONED',
                    protocol_version INTEGER DEFAULT 1,
                    firmware_version VARCHAR(24) DEFAULT '1.0.0',
                    desired_config_version INTEGER DEFAULT 1,
                    reported_config_version INTEGER DEFAULT 0,
                    sync_status VARCHAR(16) DEFAULT 'SYNCING',
                    first_seen DATETIME DEFAULT CURRENT_TIMESTAMP,
                    last_seen DATETIME DEFAULT CURRENT_TIMESTAMP,
                    updated_at DATETIME DEFAULT CURRENT_TIMESTAMP
                );

                CREATE TABLE IF NOT EXISTS device_configs (
                    device_id VARCHAR(32) PRIMARY KEY REFERENCES devices(device_id) ON DELETE CASCADE,
                    desired_json TEXT NOT NULL,
                    reported_json TEXT,
                    updated_at DATETIME DEFAULT CURRENT_TIMESTAMP
                );

                CREATE TABLE IF NOT EXISTS device_capabilities (
                    device_id VARCHAR(32) PRIMARY KEY REFERENCES devices(device_id) ON DELETE CASCADE,
                    has_voice BOOLEAN DEFAULT FALSE,
                    has_speaker BOOLEAN DEFAULT FALSE,
                    has_opus BOOLEAN DEFAULT FALSE,
                    has_wake_word BOOLEAN DEFAULT FALSE,
                    has_energy_meter BOOLEAN DEFAULT FALSE,
                    relay_channels INTEGER DEFAULT 0,
                    raw_capabilities_json TEXT
                );

                CREATE TABLE IF NOT EXISTS ota_history (
                    id INTEGER PRIMARY KEY AUTOINCREMENT,
                    device_id VARCHAR(32),
                    from_version VARCHAR(24),
                    to_version VARCHAR(24),
                    firmware_file VARCHAR(128),
                    file_sha256 VARCHAR(64),
                    status VARCHAR(16),
                    error_message TEXT,
                    started_at DATETIME DEFAULT CURRENT_TIMESTAMP,
                    completed_at DATETIME
                );

                CREATE TABLE IF NOT EXISTS telemetry_records (
                    id INTEGER PRIMARY KEY AUTOINCREMENT,
                    device_id VARCHAR(32),
                    voltage REAL,
                    current REAL,
                    power REAL,
                    energy REAL,
                    free_heap INTEGER,
                    wifi_rssi INTEGER,
                    recorded_at DATETIME DEFAULT CURRENT_TIMESTAMP
                );
                CREATE TABLE IF NOT EXISTS zones (
                    zone_id VARCHAR(32) PRIMARY KEY,
                    display_name VARCHAR(64) NOT NULL,
                    controller_id VARCHAR(32),
                    created_at DATETIME DEFAULT CURRENT_TIMESTAMP
                );
                CREATE INDEX IF NOT EXISTS idx_telemetry_dev_time ON telemetry_records(device_id, recorded_at);
                """)
                # Safe migration for existing databases
                try:
                    conn.execute("ALTER TABLE devices ADD COLUMN zone_id VARCHAR(32);")
                except Exception:
                    pass
            logger.info(f"✨ SQLite Gateway Registry initialized: {self.db_path} (WAL Mode)")
        except Exception as e:
            logger.error(f"Failed to initialize SQLite Registry at {self.db_path}: {e}")
            raise
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
